wulphred/wearabord/media/left.jpg

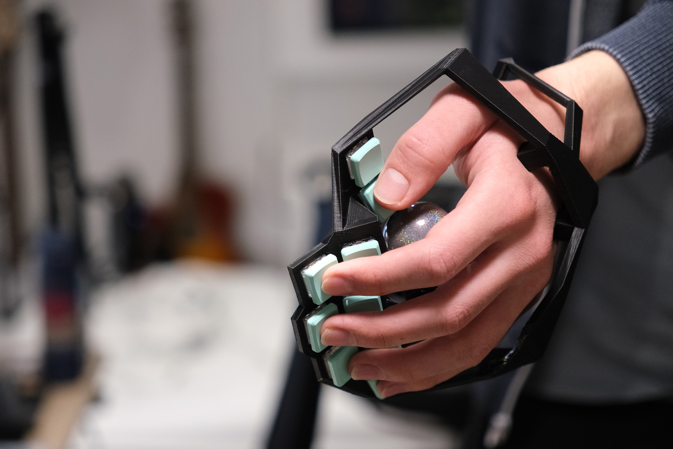
media/left.jpg
