wulphred/wearabord/media/rightold.jpg

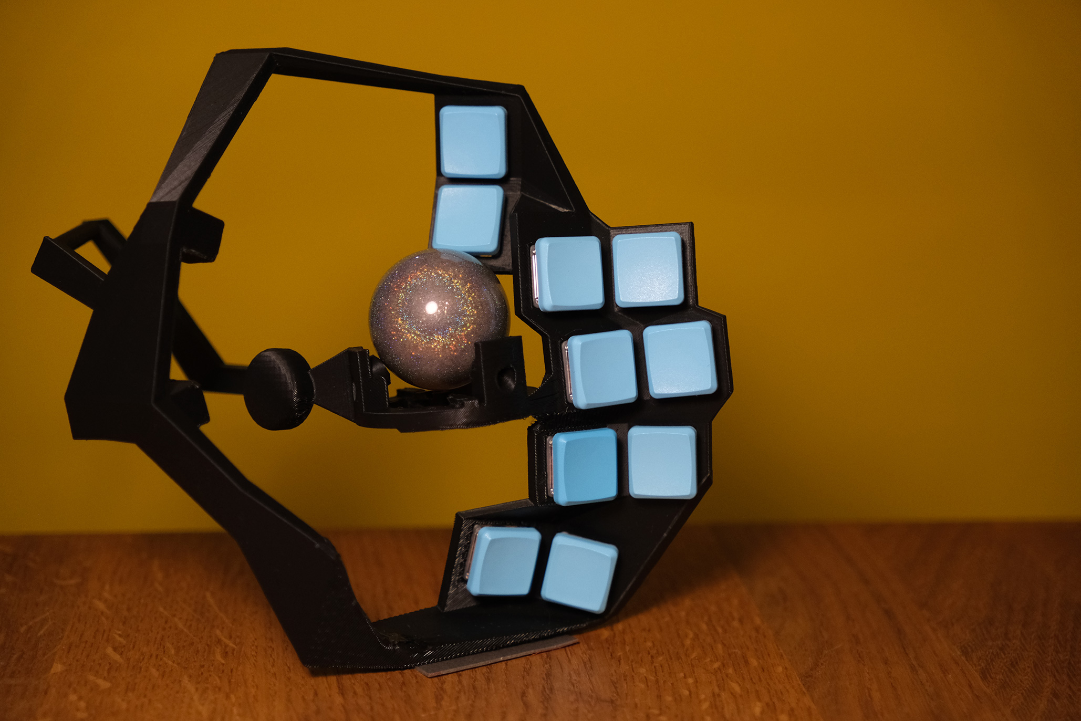
media/rightold.jpg
